aieo-product/stackchanEventBooth/baseIdea/ミニ観覧車/IMG_9115.jpeg

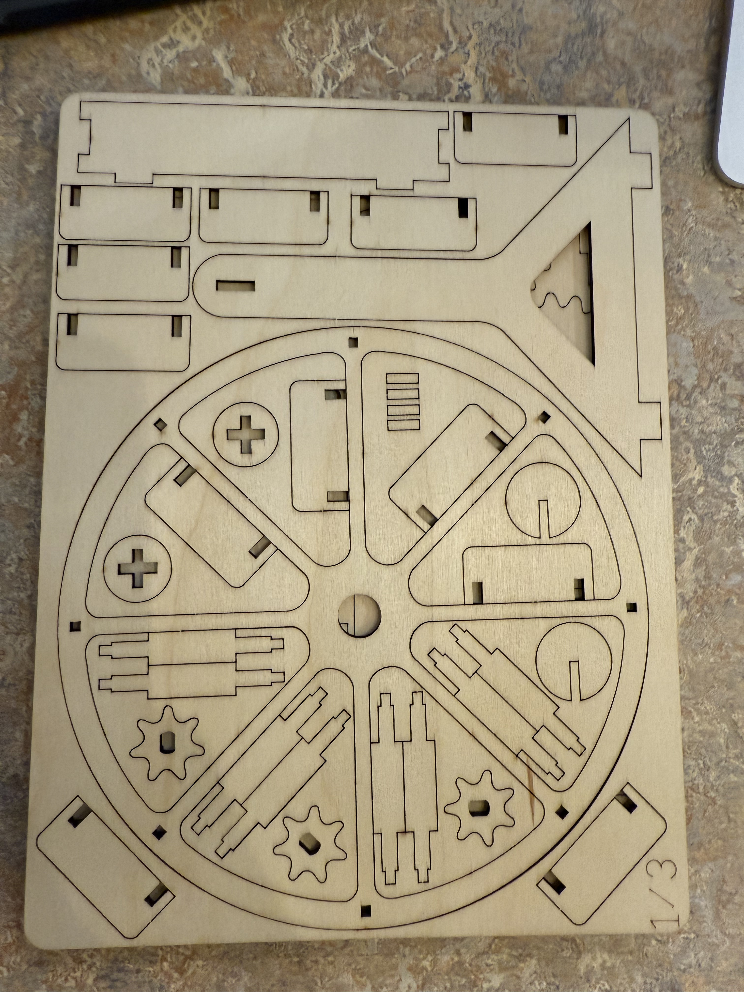
baseIdea/ミニ観覧車/IMG_9115.jpeg
