aieo-product/stackchanEventBooth/baseIdea/ミニ観覧車/IMG_9116.jpeg

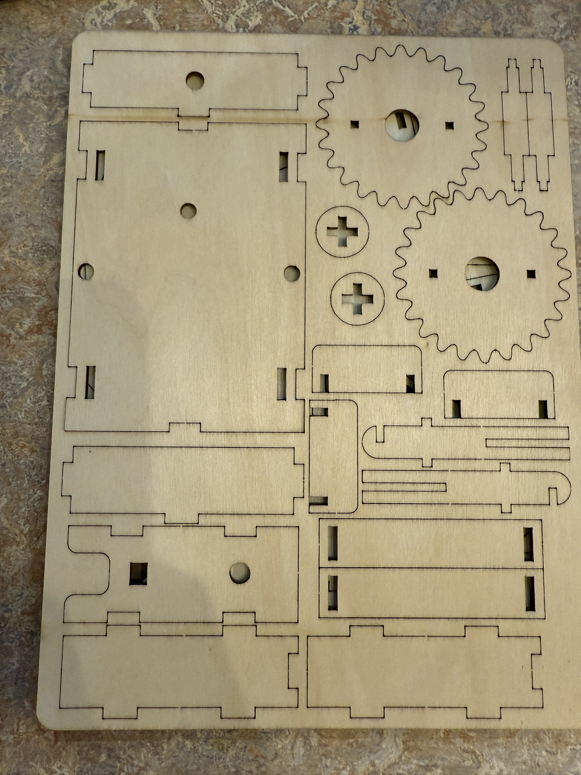
baseIdea/ミニ観覧車/IMG_9116.jpeg
