aieo-product/stackchanEventBooth/baseIdea/ミニ観覧車/IMG_9117.jpeg

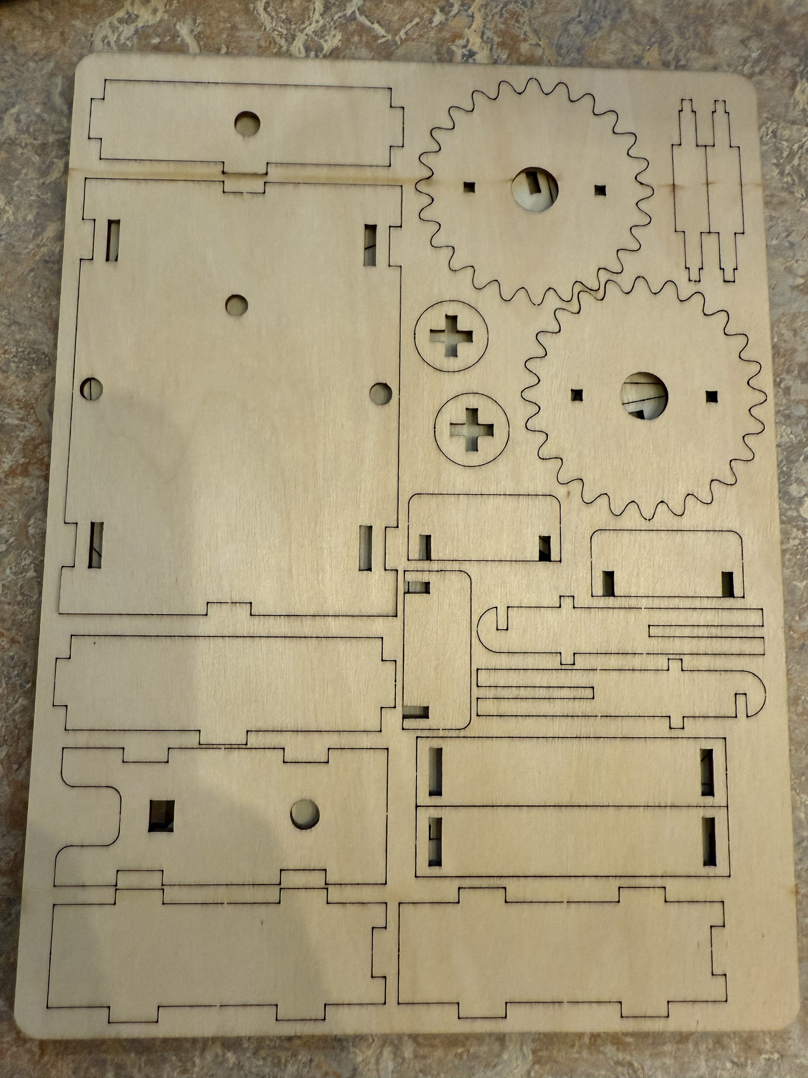
baseIdea/ミニ観覧車/IMG_9117.jpeg
