aieo-product/stackchanEventBooth/baseIdea/ミニ観覧車/IMG_9118.jpeg

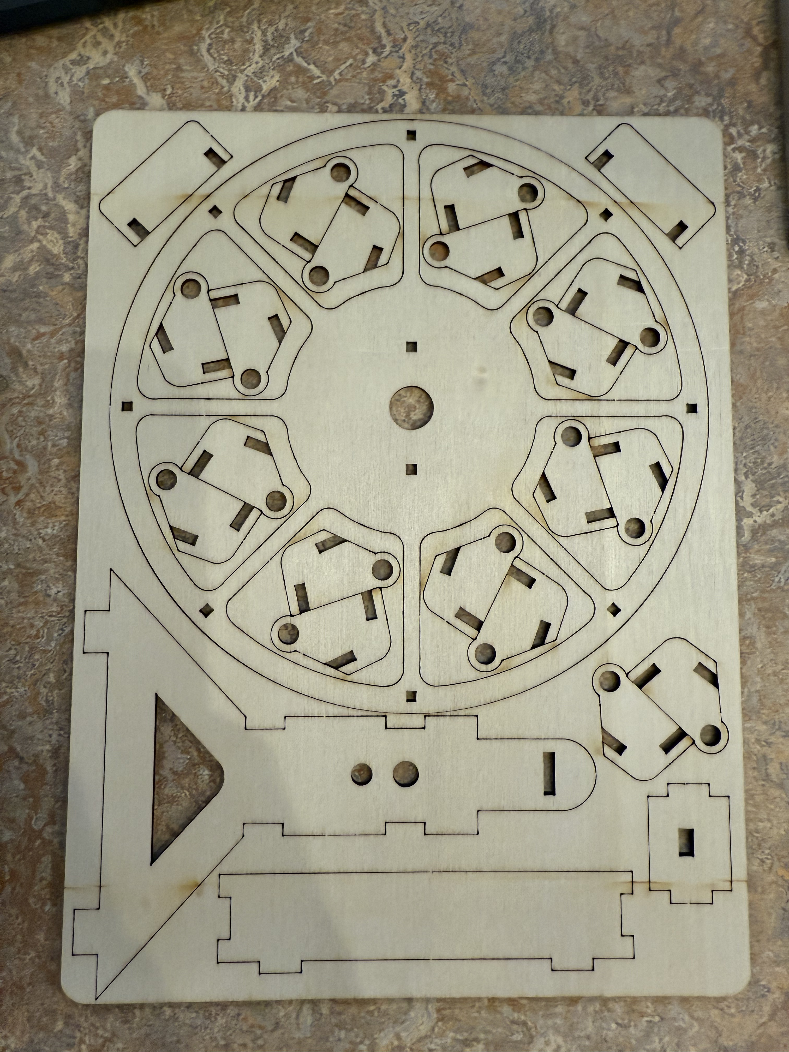
baseIdea/ミニ観覧車/IMG_9118.jpeg
