aieo-product/stackchanEventBooth/baseIdea/ミニ観覧車/IMG_9119.jpeg

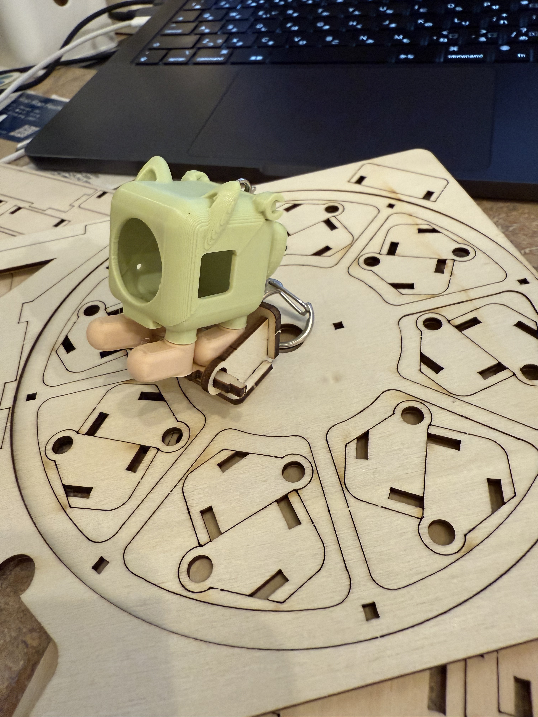
baseIdea/ミニ観覧車/IMG_9119.jpeg
