aieo-product/stackchanEventBooth/baseIdea/ミニ観覧車/IMG_9123.jpeg

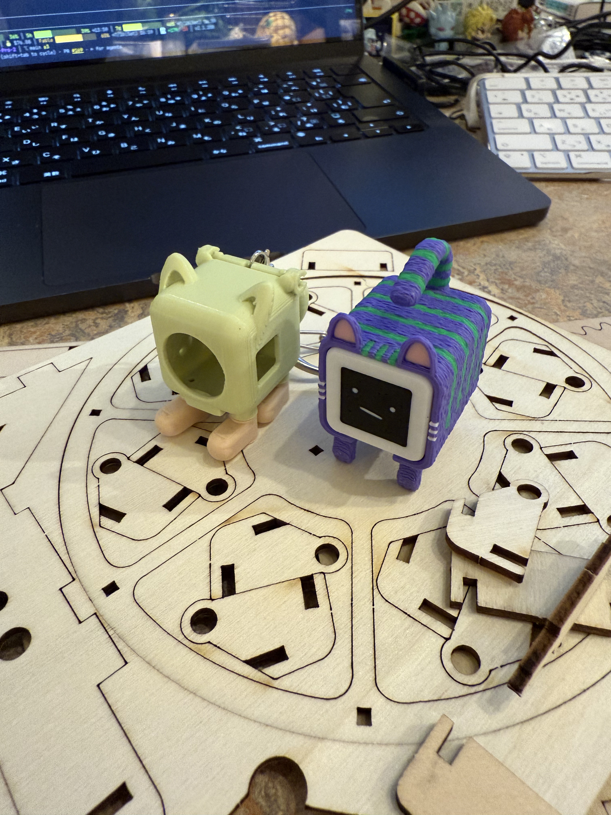
baseIdea/ミニ観覧車/IMG_9123.jpeg
