aieo-product/stackchanEventBooth/baseIdea/観覧車/IMG_9131.jpeg

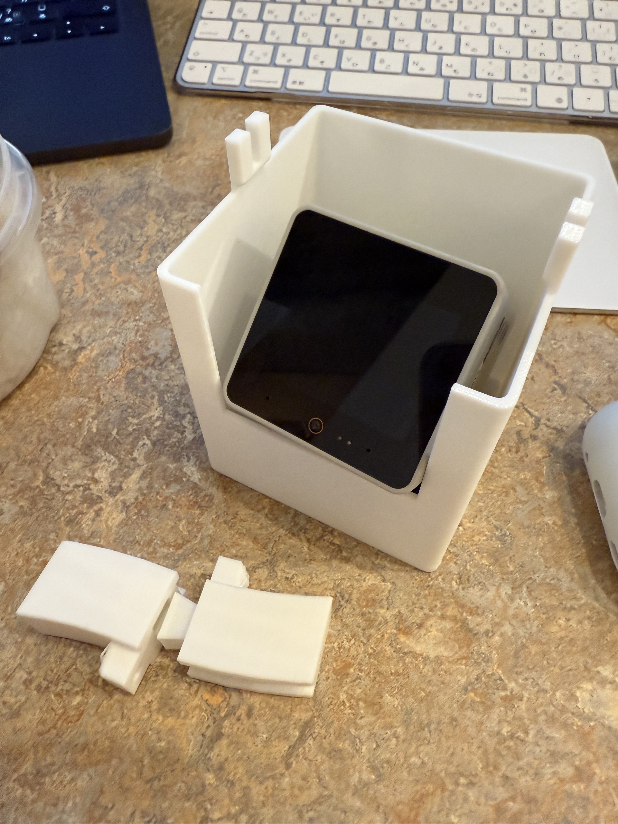
baseIdea/観覧車/IMG_9131.jpeg
