aieo-product/stackchanEventBooth/baseIdea/観覧車/IMG_9133.jpeg

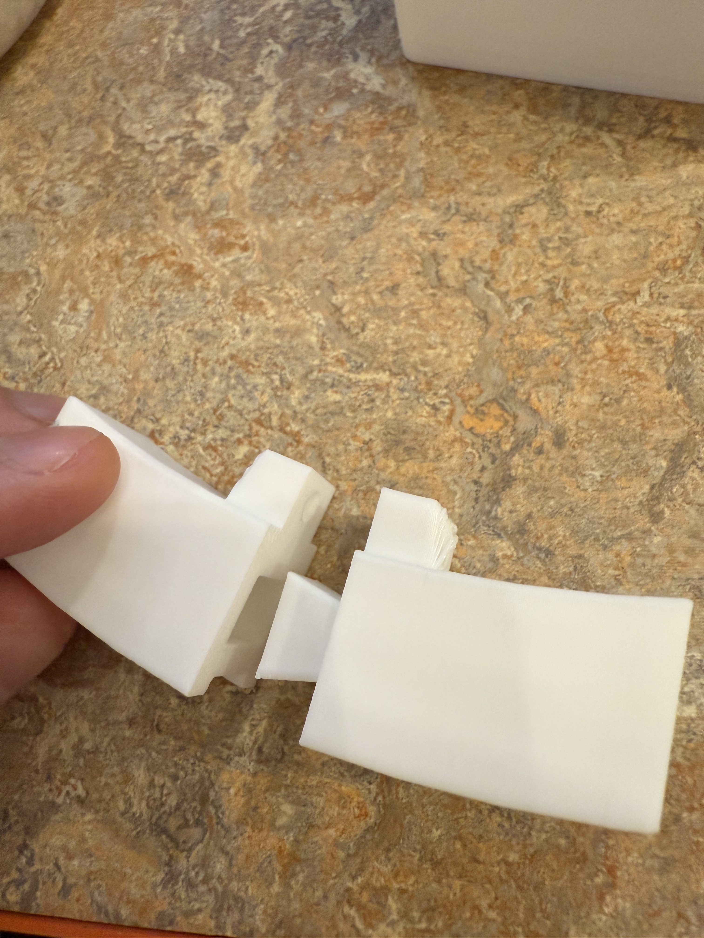
baseIdea/観覧車/IMG_9133.jpeg
