aieo-product/stackchanEventBooth/baseIdea/観覧車/IMG_9134.jpeg

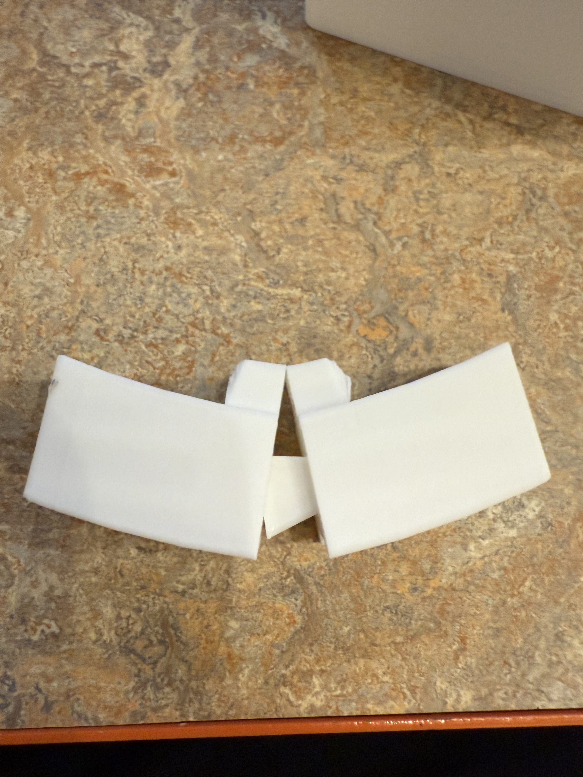
baseIdea/観覧車/IMG_9134.jpeg
