aieo-product/stackchanEventBooth/baseIdea/観覧車/IMG_9135.jpeg

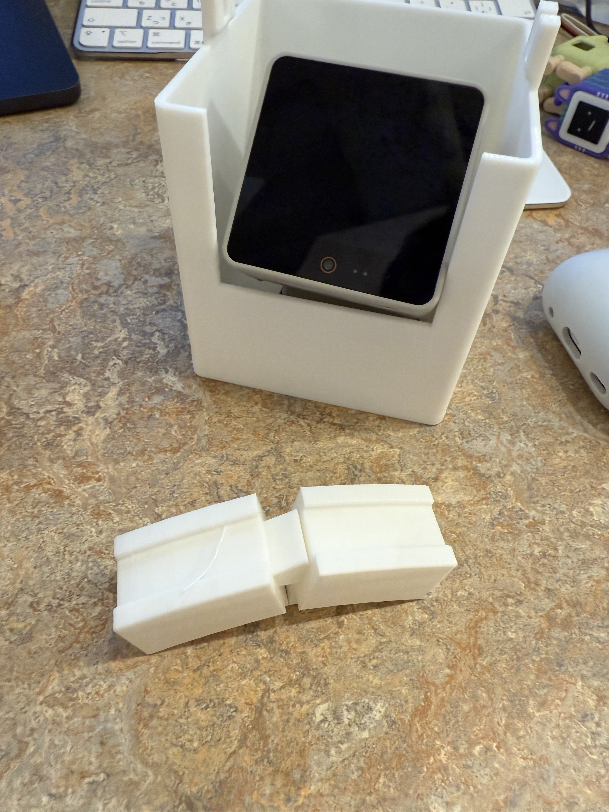
baseIdea/観覧車/IMG_9135.jpeg
