aieo-product/stackchanEventBooth/docs/public/models/ferris/crank.stl

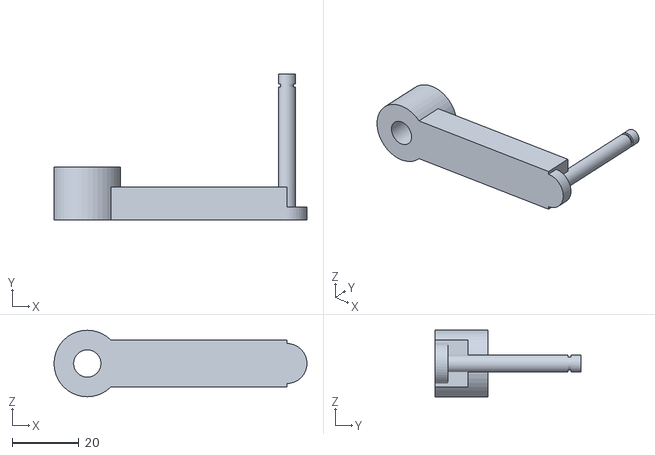
[picture p47: CAD file, 2026-07-22]
docs/public/models/ferris/crank.stl
76.0 x 44.0 x 20.0
