aieo-product/stackchanEventBooth/docs/public/models/ferris/axles.stl

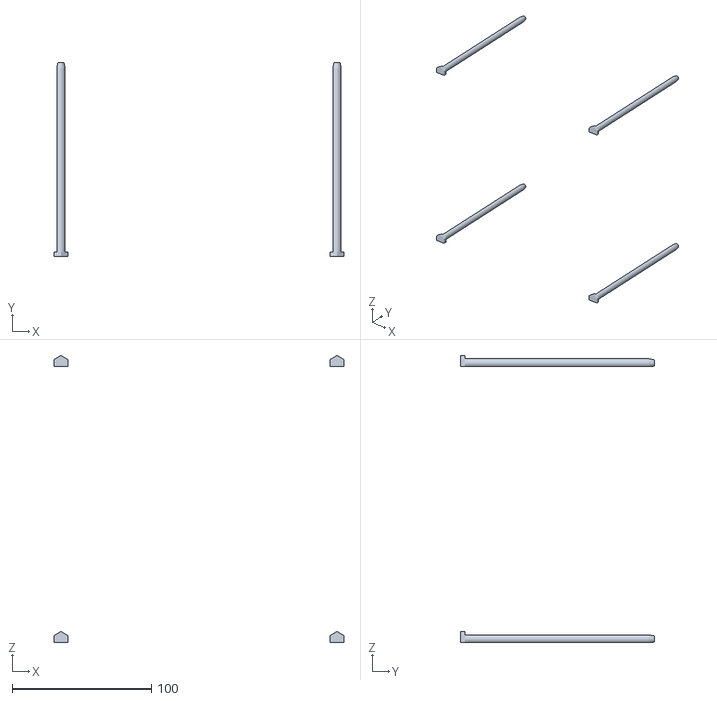
[picture p48: CAD file, 2026-07-22]
docs/public/models/ferris/axles.stl
208.0 x 139.0 x 206.0
