aieo-product/stackchanEventBooth/docs/public/models/ferris/shaft.stl

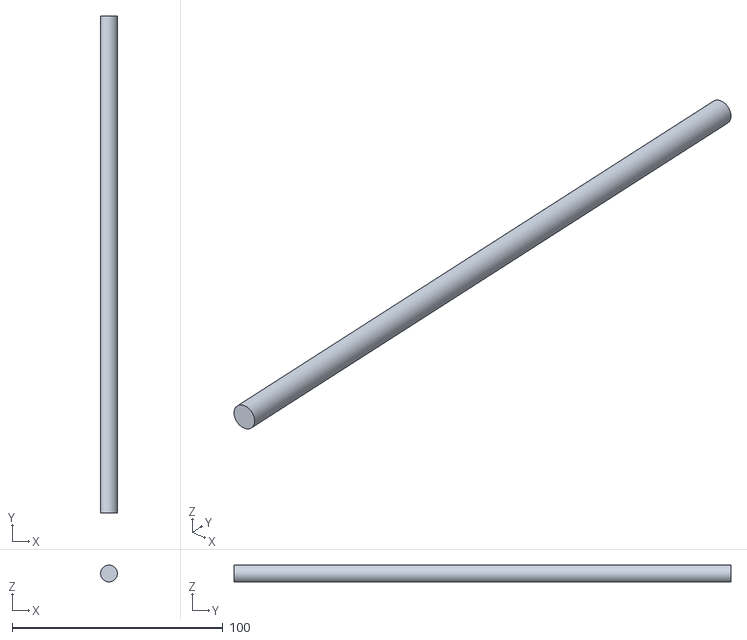
[picture p49: CAD file, 2026-07-22]
docs/public/models/ferris/shaft.stl
8.00 x 236.0 x 8.00
