aieo-product/stackchanEventBooth/docs/public/models/ferris/base.stl

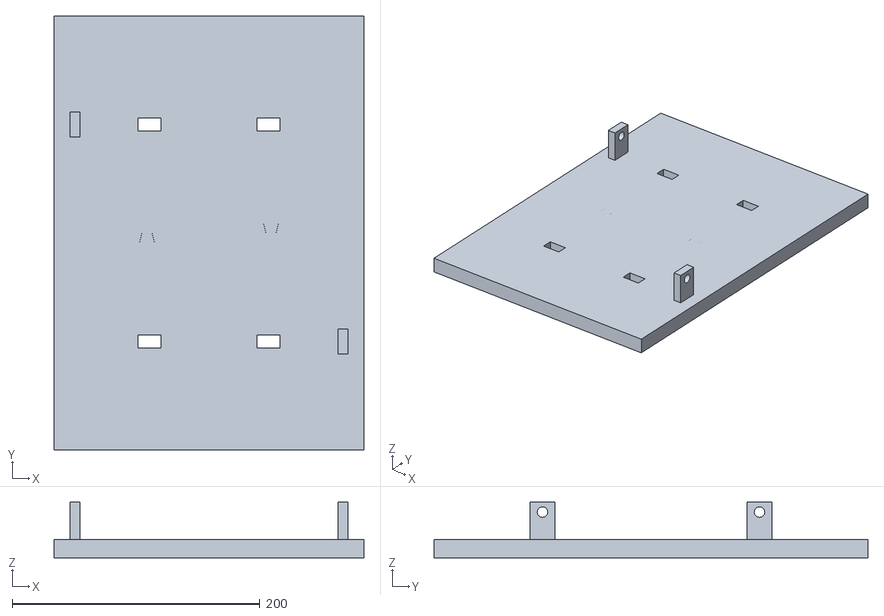
[picture p50: CAD file, 2026-07-16]
docs/public/models/ferris/base.stl
250.0 x 350.0 x 45.0
