aieo-product/stackchanEventBooth/cad/booth/wall_panel.scad

// booth/wall_panel.scad
// Wall panel 150 x 125 x 5, shared base + three variants.
//   variant = "blackboard" : framed shallow recess (green paper backing)
//   variant = "window"     : 2x2 window openings + back rebate for sky paper
//   variant = "board"      : cork-style frame + pin-hole grid (bulletin board)
// Select at CLI:  openscad -D 'variant="window"' -o wall-window.stl wall_panel.scad
// Panel lies in X-Y (x=150 wide, y=125 tall, z=5 thick); two stand tabs at the
// bottom edge drop into the stand slots.

include <../params.scad>;
use <../lib/dovetail.scad>;

variant = "blackboard";       // overridden from the Makefile

fx = wall_frame;              // frame width
ix0 = fx; ix1 = wall_x - fx;  // interior x range
iy0 = fx; iy1 = wall_y - fx;  // interior y range

module base_panel() {
    // panel body
    translate([0, 0, 0]) cube([wall_x, wall_y, wall_t]);
    // two stand tabs on the bottom edge (protrude -y)
    for (sx = [-1, 1])
        translate([wall_x/2 + sx * 40 - wall_tab_w/2, -wall_tab_h + 0.01, 0])
            cube([wall_tab_w, wall_tab_h, wall_t]);
}

module blackboard() {
    difference() {
        base_panel();
        // shallow recess on the front for a green paper insert
        translate([ix0, iy0, wall_t - bb_recess_d])
            cube([ix1 - ix0, iy1 - iy0, bb_recess_d + 0.1]);
    }
}

module window() {
    difference() {
        base_panel();
        // 2x2 through openings separated by a cross mullion
        cx = (ix0 + ix1) / 2;
        cy = (iy0 + iy1) / 2;
        for (px = [[ix0, cx - win_mullion/2], [cx + win_mullion/2, ix1]])
            for (py = [[iy0, cy - win_mullion/2], [cy + win_mullion/2, iy1]])
                translate([px[0], py[0], -1])
                    cube([px[1] - px[0], py[1] - py[0], wall_t + 2]);
        // back rebate for the sky-image paper
        translate([ix0 - 2, iy0 - 2, -0.01])
            cube([ix1 - ix0 + 4, iy1 - iy0 + 4, win_inset]);
    }
}

module board() {
    difference() {
        union() {
            base_panel();
            // raised cork frame
            difference() {
                translate([ix0 - cork_frame, iy0 - cork_frame, wall_t])
                    cube([ix1 - ix0 + 2 * cork_frame, iy1 - iy0 + 2 * cork_frame, 1.5]);
                translate([ix0, iy0, wall_t - 0.01])
                    cube([ix1 - ix0, iy1 - iy0, 2]);
            }
        }
        // pin-hole grid (blind holes)
        for (i = [0 : pin_grid - 1])
            for (j = [0 : pin_grid - 1])
                translate([ix0 + (i + 0.5) * (ix1 - ix0) / pin_grid,
                           iy0 + (j + 0.5) * (iy1 - iy0) / pin_grid,
                           wall_t - pin_hole_depth])
                    cylinder(d = pin_hole_d, h = pin_hole_depth + 0.1);
    }
}

module screen() {
    // 7/23 LT-meetup: whiteboard / projector screen. The printed slide (paper)
    // drops in from the TOP edge behind the front frame, so slides can be
    // swapped during the event. Paper cut size: ~140 x 118 (see channel).
    difference() {
        union() {
            base_panel();
            // whiteboard marker-tray lip along the front bottom edge
            translate([ix0, 2, wall_t])
                cube([ix1 - ix0, scr_tray_d, scr_tray_h]);
        }
        // window opening through the front frame layer
        translate([ix0, iy0, wall_t - scr_front_t])
            cube([ix1 - ix0, iy1 - iy0, scr_front_t + 0.1]);
        // paper channel: wider than the window, open through the top edge
        translate([ix0 - scr_slot_margin, iy0 - scr_slot_margin,
                   wall_t - scr_front_t - scr_slot_t])
            cube([ix1 - ix0 + 2 * scr_slot_margin,
                  wall_y - iy0 + scr_slot_margin + 1,
                  scr_slot_t]);
    }
}

module screen_half(side) {
    // 7/23 rev2: the screen spans TWO tiles (300 wide) as an L+R pair joined
    // by half-depth dovetails on the seam edge (z 0..2.4, below the paper
    // channel z 2.6..3.8 -> one continuous channel across both halves).
    // ONE paper sheet 288 x 117 (A4 landscape) slides in from the top.
    // L = frame on the left/top/bottom, seam on +X. R = mirror (seam on -X).
    seam_ten_y = [25, 62.5, 100];        // dovetail centres up the seam edge
    difference() {
        union() {
            base_panel();
            // marker-tray lip (stops short of the seam by 2)
            if (side == "L") translate([ix0, 2, wall_t]) cube([wall_x - ix0 - 2, scr_tray_d, scr_tray_h]);
            else             translate([2, 2, wall_t])   cube([ix1 - 2, scr_tray_d, scr_tray_h]);
            // half-depth dovetail tenons on the L seam edge
            if (side == "L")
                for (yy = seam_ten_y)
                    translate([wall_x, yy, 0]) rotate([0, 0, -90]) dovetail_tenon(h = 2.4);
        }
        // window opening through the front frame, open through the seam edge
        if (side == "L") translate([ix0, iy0, wall_t - scr_front_t]) cube([wall_x - ix0 + 1, iy1 - iy0, scr_front_t + 0.1]);
        else             translate([-1,  iy0, wall_t - scr_front_t]) cube([ix1 + 1,          iy1 - iy0, scr_front_t + 0.1]);
        // paper channel, open through the seam edge AND the top edge
        if (side == "L")
            translate([ix0 - scr_slot_margin, iy0 - scr_slot_margin, wall_t - scr_front_t - scr_slot_t])
                cube([wall_x - ix0 + scr_slot_margin + 1, wall_y - iy0 + scr_slot_margin + 1, scr_slot_t]);
        else
            translate([-1, iy0 - scr_slot_margin, wall_t - scr_front_t - scr_slot_t])
                cube([ix1 + scr_slot_margin + 1, wall_y - iy0 + scr_slot_margin + 1, scr_slot_t]);
        // half-depth dovetail mortises on the R seam edge
        if (side == "R")
            for (yy = seam_ten_y)
                translate([0, yy, 0]) rotate([0, 0, 90]) dovetail_mortise(h = 2.55);
    }
}

module plainwall() {
    // 7/23: plain office wall - flat panel with two shallow horizontal
    // panel-seam grooves (shadow lines, no painting needed)
    difference() {
        base_panel();
        for (gy = [42, 84])
            translate([-1, gy - 0.3, wall_t - 0.6])
                cube([wall_x + 2, 0.6, 0.7]);
    }
}

if (variant == "plain")           plainwall();
else if (variant == "screen-l")   screen_half("L");
else if (variant == "screen-r")   screen_half("R");
else if (variant == "window")     window();
else if (variant == "board")      board();
else if (variant == "screen")     screen();
else                              blackboard();
